microcontrollersig/reverse-engineer-led-signs/images/IMG_20170827_141344.jpg

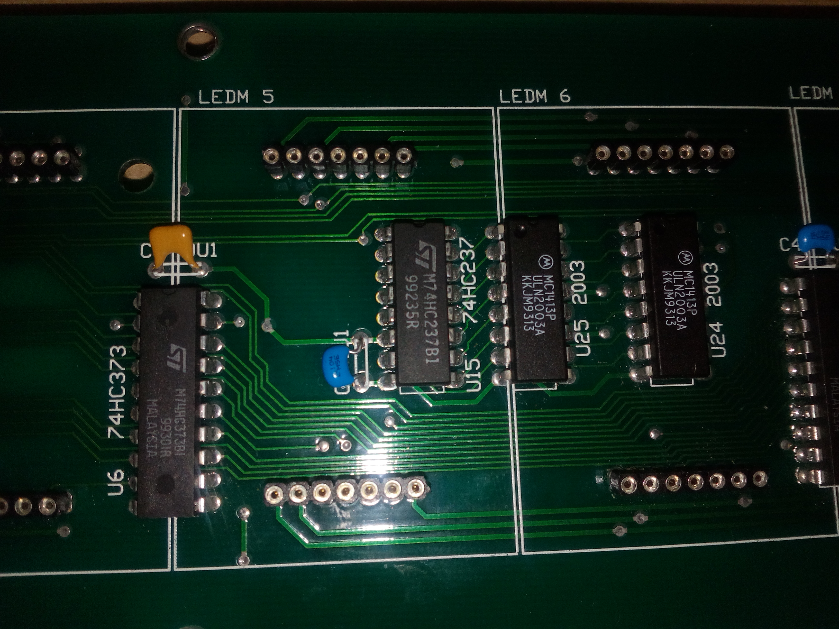
images/IMG_20170827_141344.jpg
