microcontrollersig/reverse-engineer-led-signs/images/IMG_20170827_141502.jpg

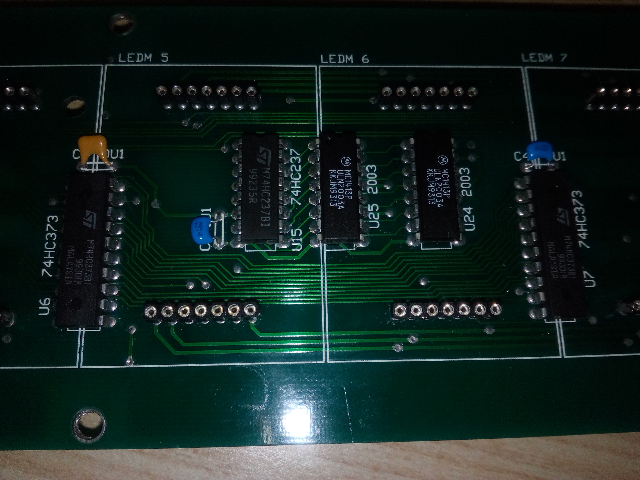
images/IMG_20170827_141502.jpg
