microcontrollersig/reverse-engineer-led-signs/images/IMG_20170827_141822.jpg

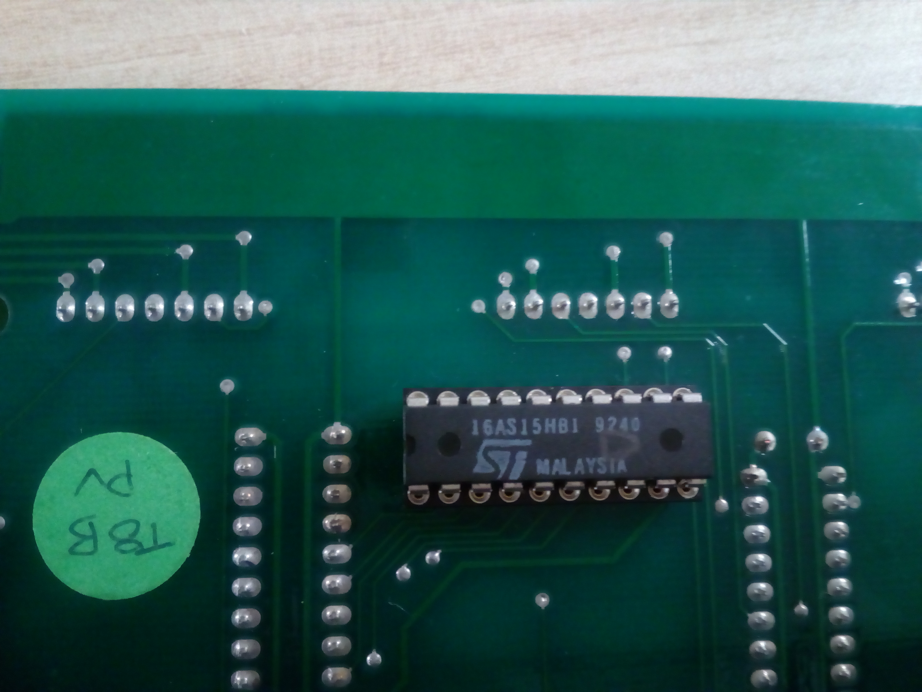
images/IMG_20170827_141822.jpg
