microcontrollersig/reverse-engineer-led-signs/images/IMG_20170827_141834.jpg

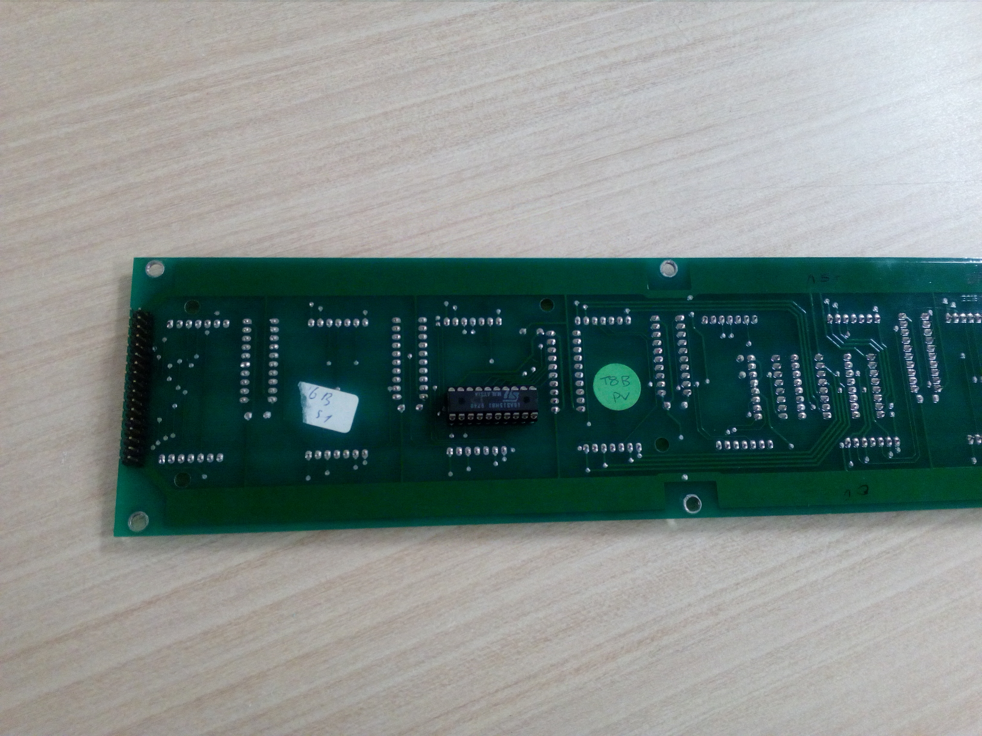
images/IMG_20170827_141834.jpg
