microcontrollersig/reverse-engineer-led-signs/images/IMG_20170827_141844.jpg

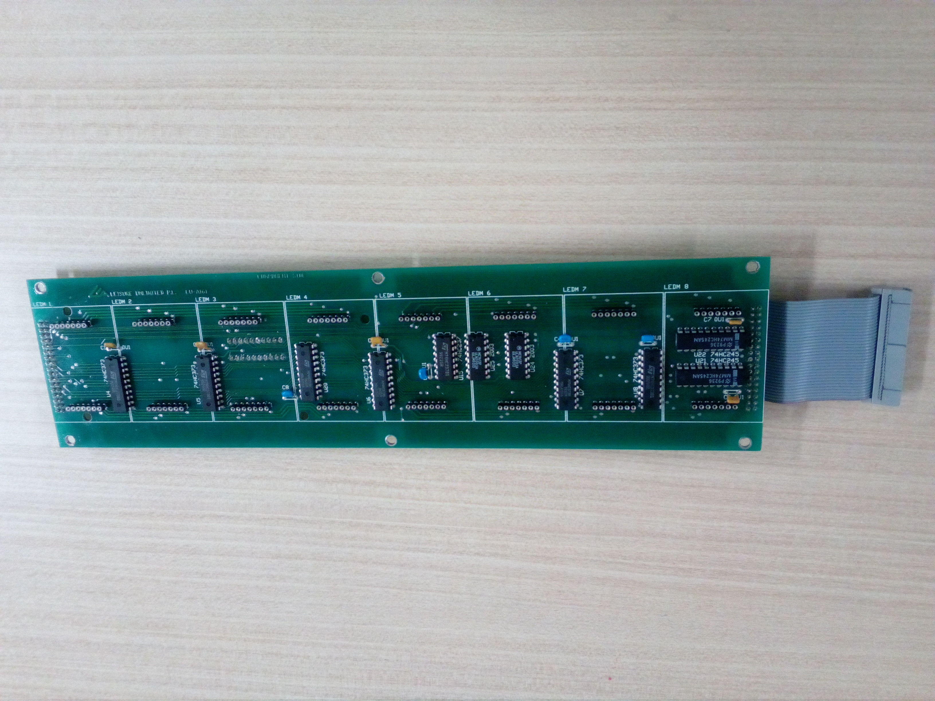
images/IMG_20170827_141844.jpg
