microcontrollersig/reverse-engineer-led-signs/images/IMG_20170827_141917.jpg

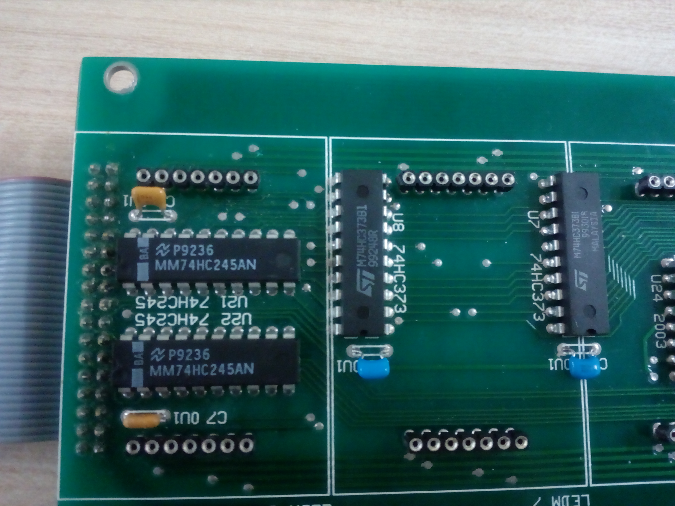
images/IMG_20170827_141917.jpg
