microcontrollersig/reverse-engineer-led-signs/images/IMG_20170827_141923.jpg

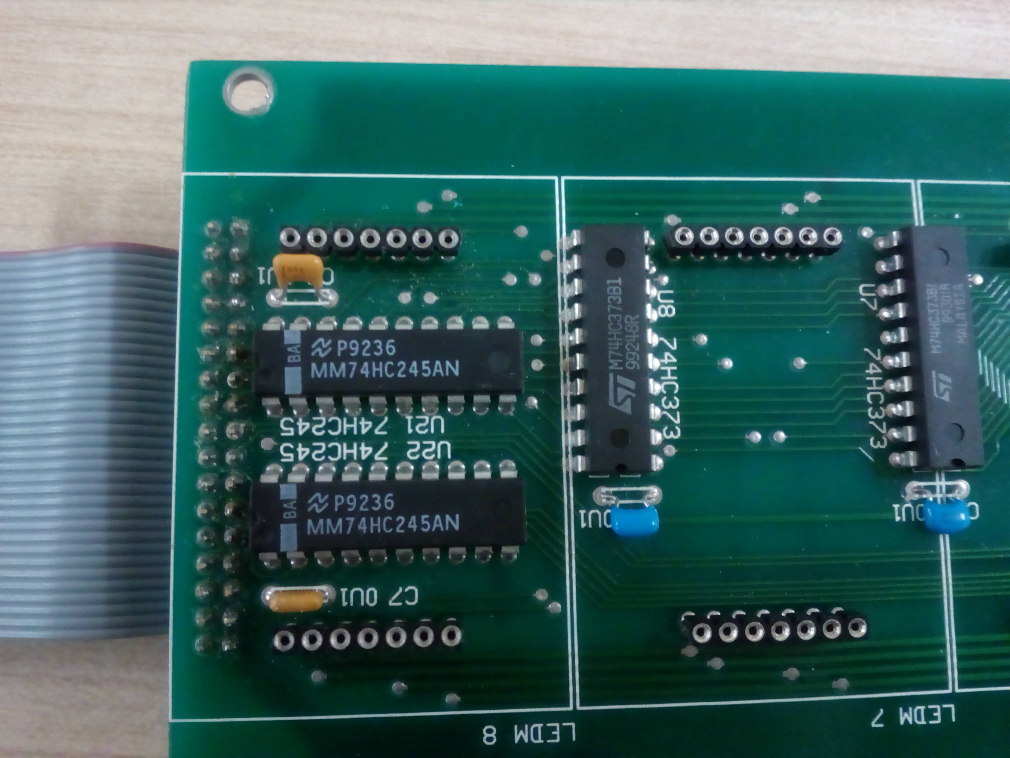
images/IMG_20170827_141923.jpg
