microcontrollersig/reverse-engineer-led-signs/images/IMG_20170827_142001.jpg

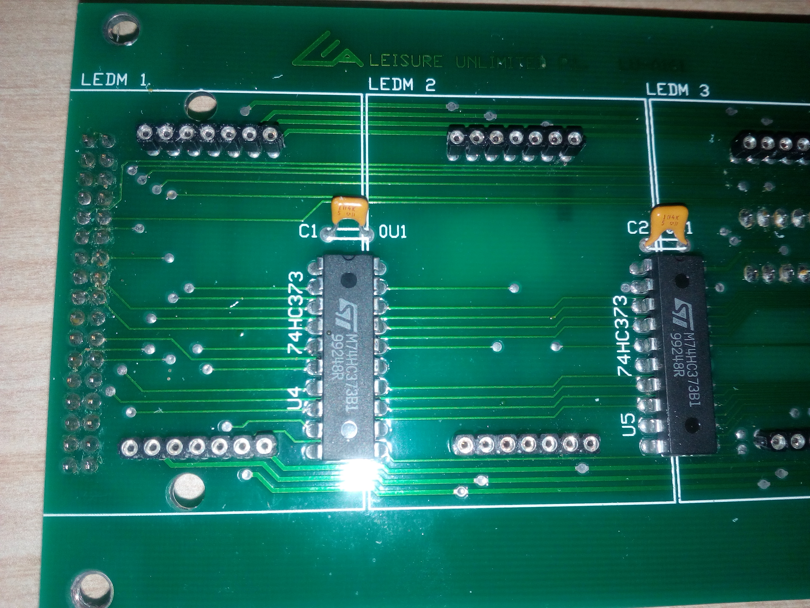
images/IMG_20170827_142001.jpg
