microcontrollersig/reverse-engineer-led-signs/images/IMG_20170827_142012.jpg

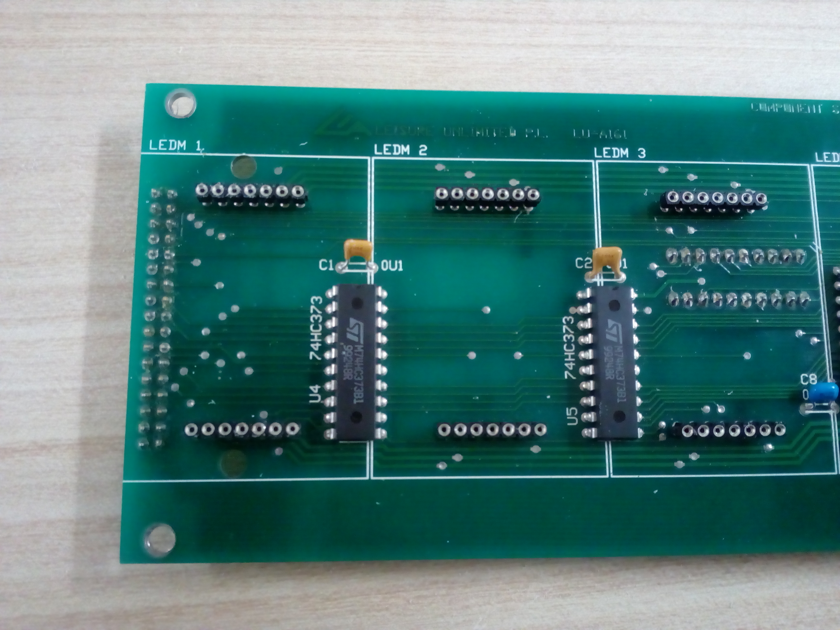
images/IMG_20170827_142012.jpg
