microcontrollersig/reverse-engineer-led-signs/images/IMG_20170827_142103.jpg

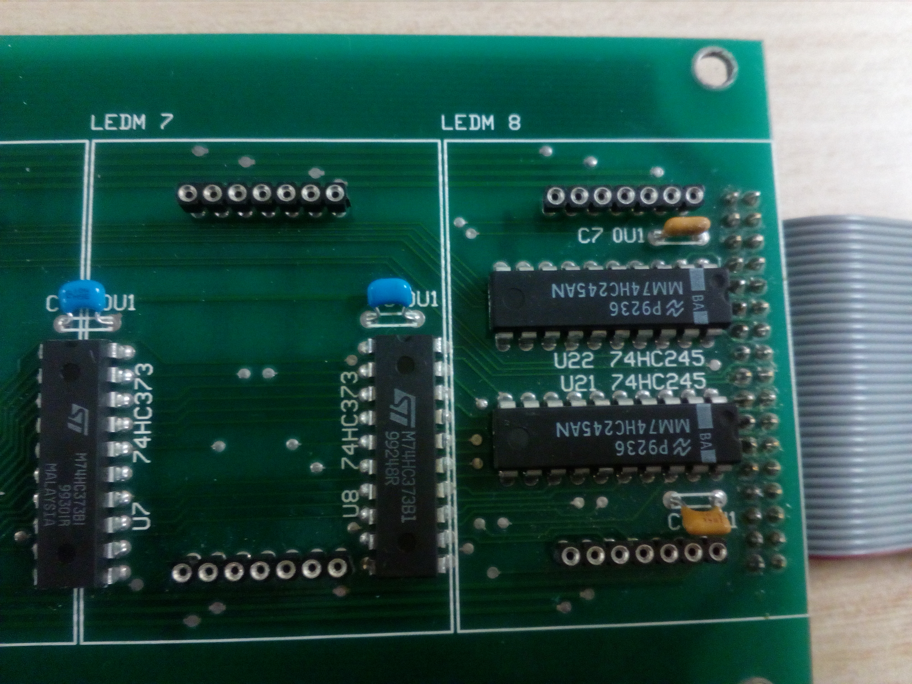
images/IMG_20170827_142103.jpg
